Netdex/rubiks-cube-solver/code/experimental/00.jpg

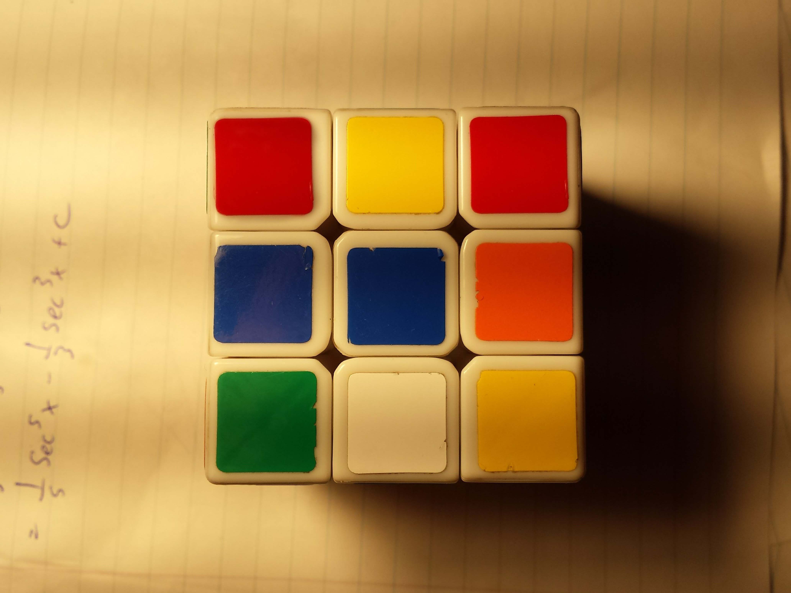
code/experimental/00.jpg
