Netdex/rubiks-cube-solver/code/experimental/01.jpg

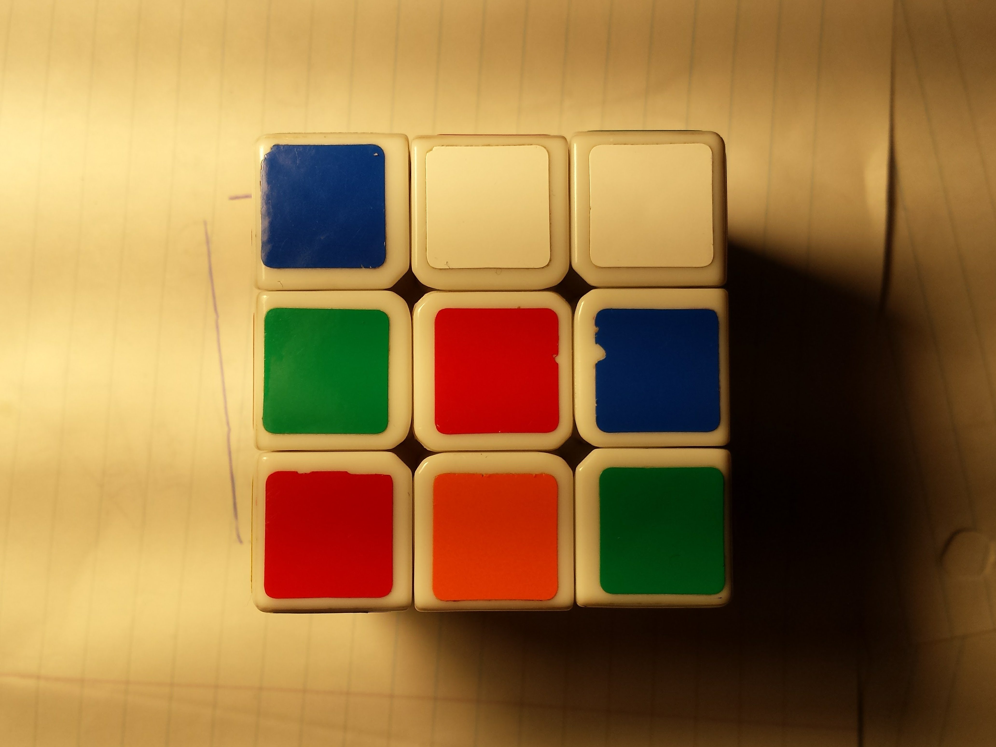
code/experimental/01.jpg
