Netdex/rubiks-cube-solver/code/experimental/02.jpg

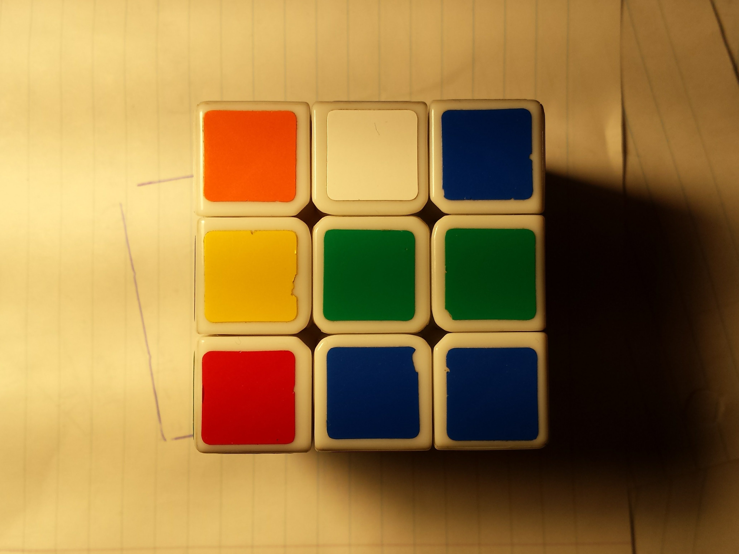
code/experimental/02.jpg
