Netdex/rubiks-cube-solver/code/experimental/03.jpg

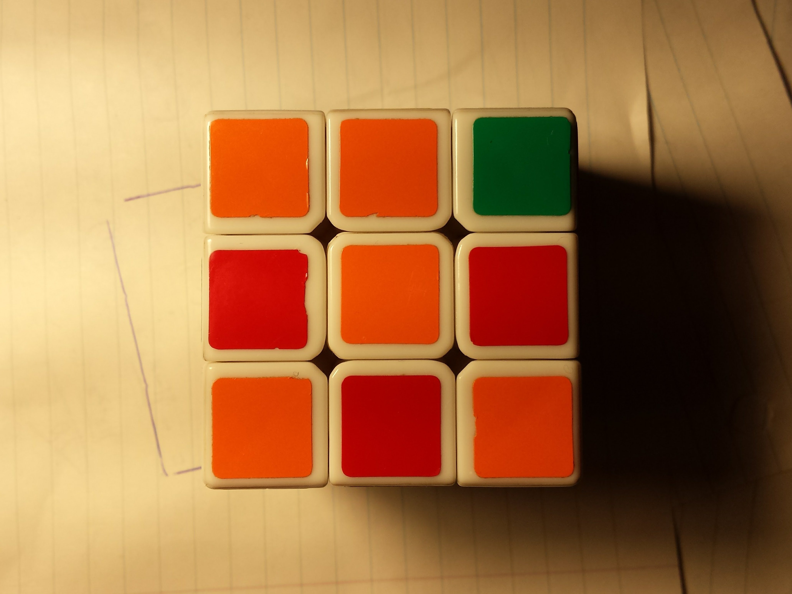
code/experimental/03.jpg
