Netdex/rubiks-cube-solver/code/experimental/04.jpg

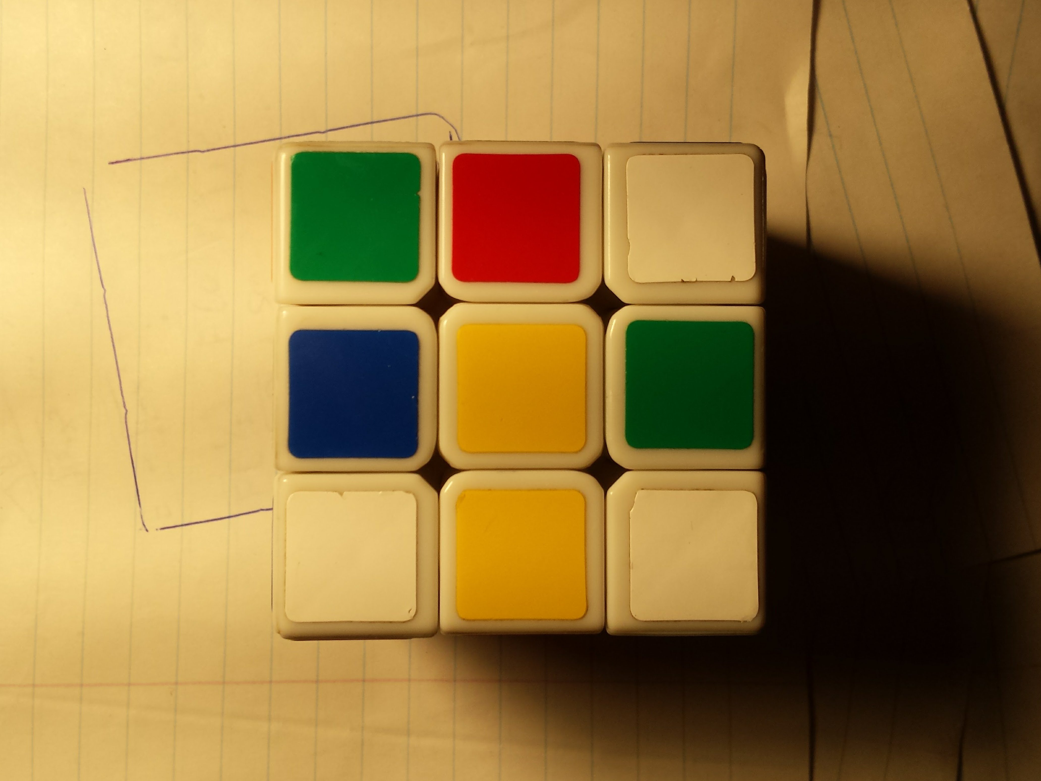
code/experimental/04.jpg
