Netdex/rubiks-cube-solver/code/include/motor.h

#ifndef MOTOR_H
#define MOTOR_H


#include <BBBiolib.h>

#include "util/nsleep.h" 

#define DELAY       750000
#define OVERSHOOT   48
 
#define DIR_CW      0
#define DIR_CCW     1
#define DIR_DCW     2
#define DIR_DCCW    3

typedef struct {
    int bank;
    int pin1;
    int pin2;
    int pin3;
    int pin4;
} motor;

void motor_init(motor m);
void motor_free(motor m);
void step(int step, motor m);
void steps(int steps, motor m);
void q_turn(motor m, int dir);
void q_turn_d(motor m1, motor m2, int dir1, int dir2);
void h_turn(motor m, int dir);
void h_turn_d(motor m1, motor m2, int dir1, int dir2);

#endif
