Netdex/rubiks-cube-solver/code/include/bbb_gpio.h

#ifndef BBB_GPIO_H
#define BBB_GPIO_H

#define BBB_IN 0
#define BBB_OUT 1

#define BBB_LO 0
#define BBB_HI 1

void exp_pin(int n);
void set_dir(int n, int dir);
int read_val(int n);
void write_val(int n, int val);

#endif
